maki-makirou/Measuring_Aquatic_Ultrasonic_Level_Instrument/img/IMG_6523.JPG

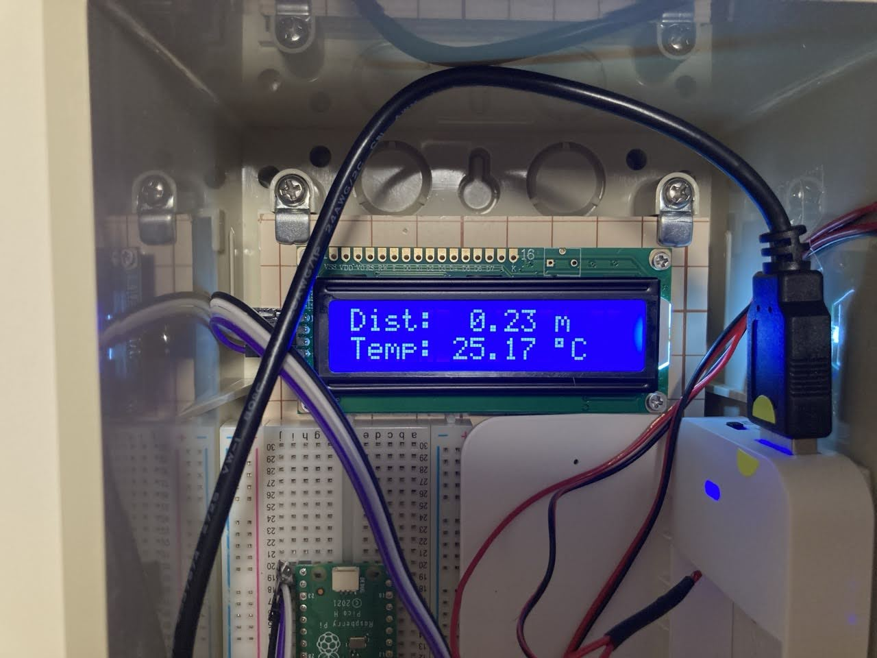
img/IMG_6523.JPG
