maki-makirou/Measuring_Aquatic_Ultrasonic_Level_Instrument/Know-how/img/IMG_6432.JPG

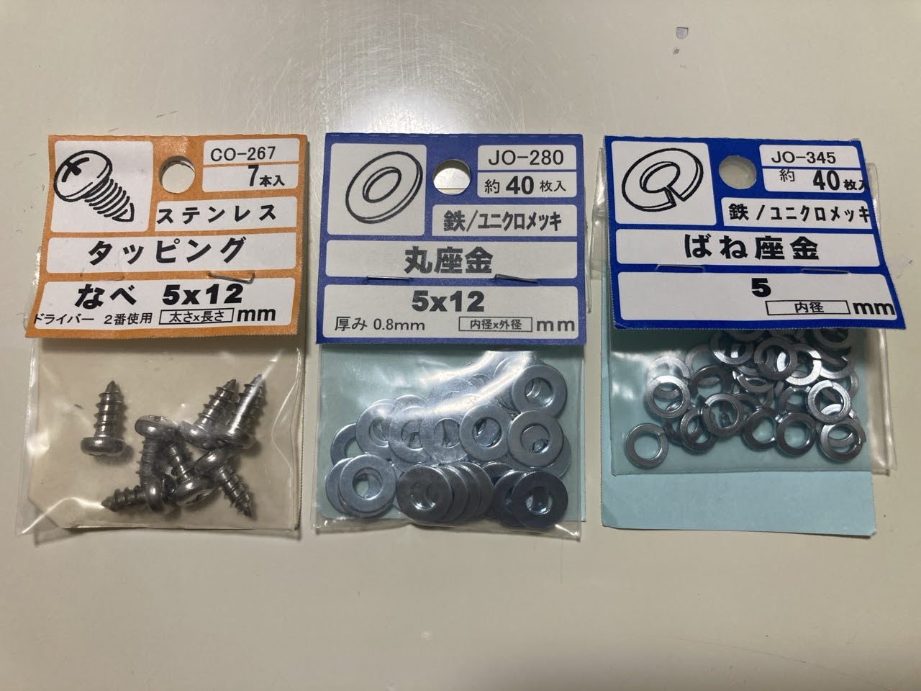
Know-how/img/IMG_6432.JPG
