maki-makirou/Measuring_Aquatic_Ultrasonic_Level_Instrument/MAULI_202501/img/202210_B.png

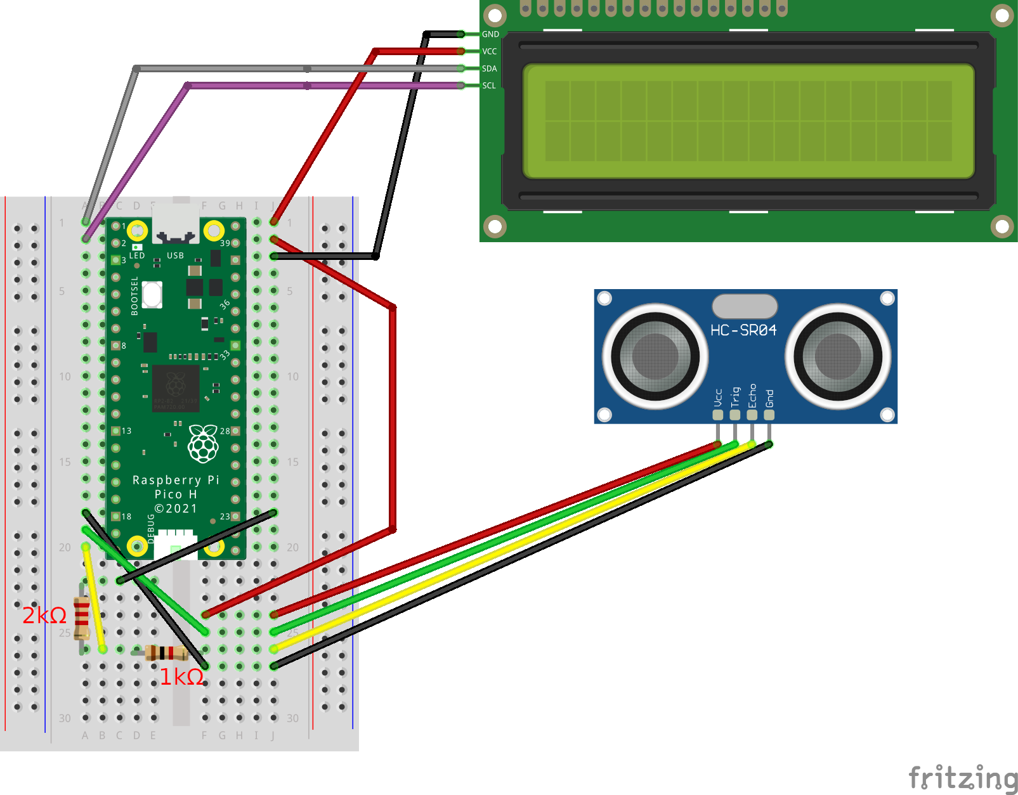
MAULI_202501/img/202210_B.png
