maki-makirou/Measuring_Aquatic_Ultrasonic_Level_Instrument/MAULI_202501/img/IMG_6465.JPG

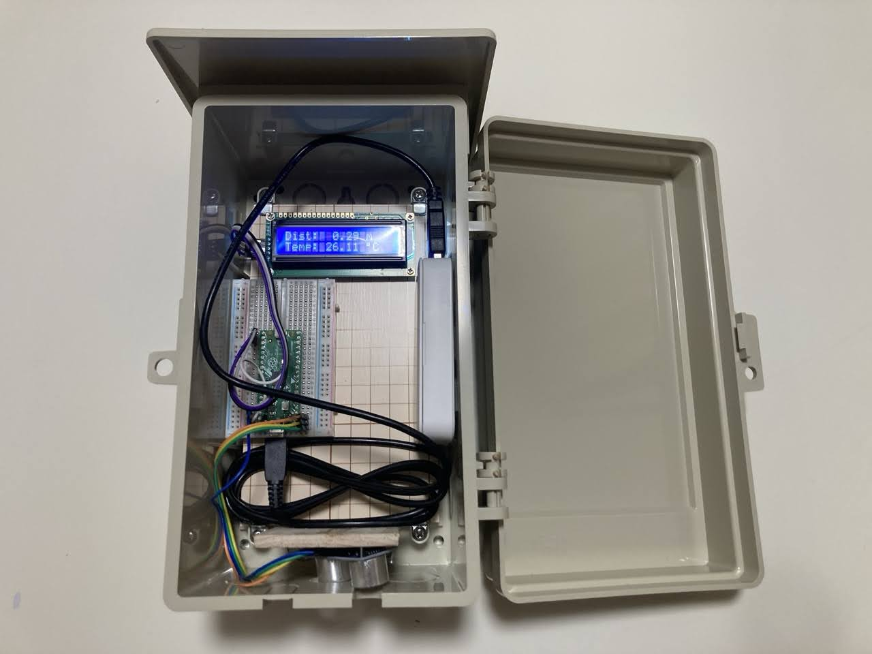
MAULI_202501/img/IMG_6465.JPG
