maki-makirou/Measuring_Aquatic_Ultrasonic_Level_Instrument/MAULI_202501/img/MAULI_202501_K.png

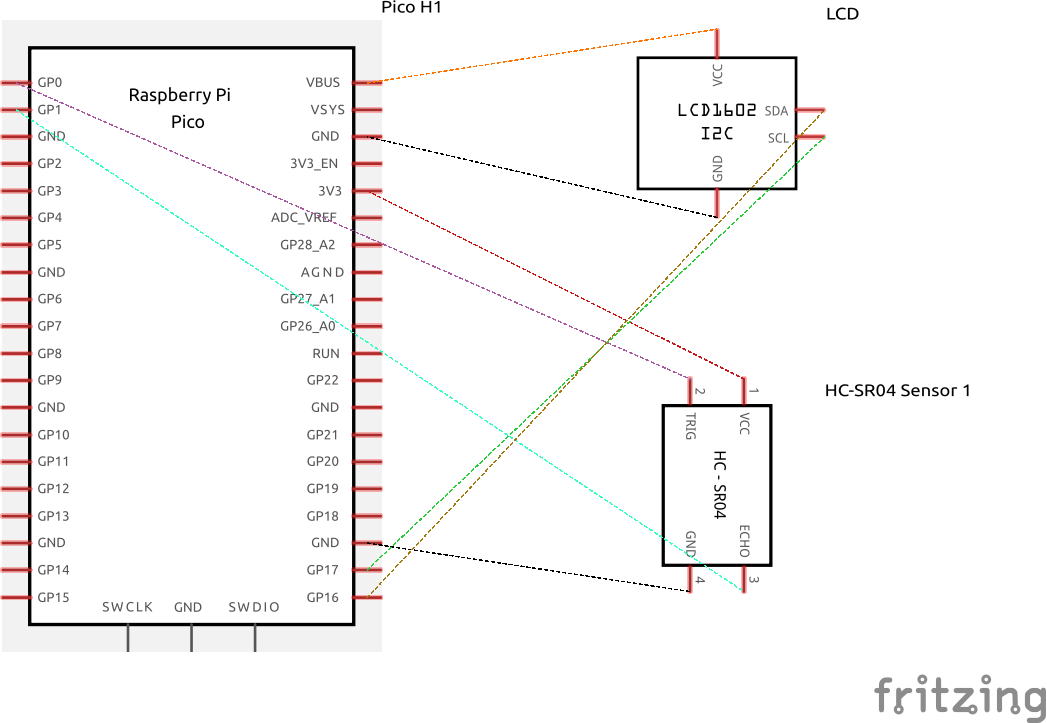
MAULI_202501/img/MAULI_202501_K.png
