maki-makirou/Measuring_Aquatic_Ultrasonic_Level_Instrument/MAULI_202501/Woodworking/img/IMG_6422.JPG

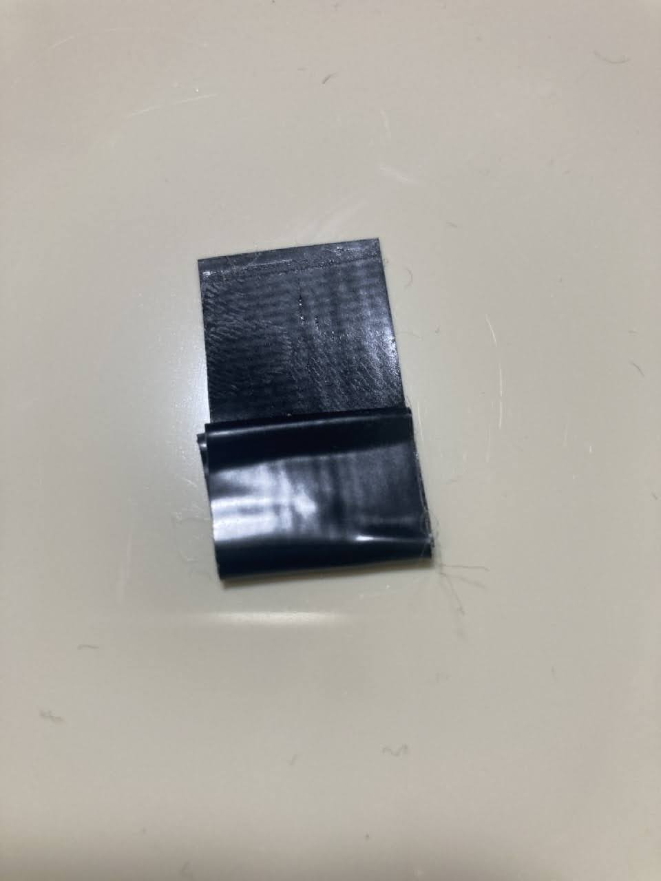
MAULI_202501/Woodworking/img/IMG_6422.JPG
